Resinchem/Ultimate-Bedside-Lamp/docs/commands.md

---
layout: default
title: Controller Commands
parent: General System Use
nav_order: 3
---

# Controller Commands
{: .no_toc }

---

<p align="center">
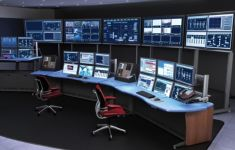
[picture p59: docs/images/commands_01.jpg]
Controller Commands Header
  
</p>

Under normal operation, the system firmware abstracts the hardware so you don't have to worry about which of the three ESP-based controllers you are interacting with. However, **Controller Commands** are the exception—these functions generally apply *only* to the specific controller currently active in your browser.

> **💡 Identifying the Active Controller**<br>As detailed in the [Web Application Overview]({{ '/webapp' | relative_url }}), look for these indicators to know which unit you are controlling:
> * **Primary Controller:** Light Gray background; assigned Device Name in the header.
> * **Display Controller:** Pale Yellow background; "Display" in the header/browser tab.
{: .note }

---

## Primary Controller Commands
These are found at the bottom of the primary controller’s web page. All **yellow** buttons in this section impact only the _primary_ controller.

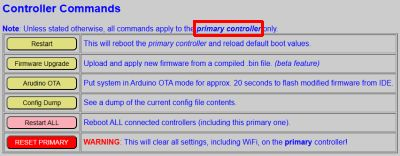
[picture p60: docs/images/commands_02.jpg]
Primary Commands Interface


* **Restart:** Reboots the primary controller only. Other units remain operational, though some cross-device features will pause until the primary unit finishes its boot sequence.

* **Firmware Upgrade:** Accesses the update page for the primary controller. 
    > **⚠️ Warning**<br>Installing the wrong firmware file on the wrong controller will break your system. See [Installing Updates]({{ '/firmwareupdates' | relative_url }}) before proceeding.
    {: .warning }

* **Arduino OTA:** Enables "Over-the-Air" programming for 20 seconds, allowing you to begin flashing code directly from the Arduino IDE. See [Modifying the Firmware]({{ '/modifications' | relative_url }}).
* **Config Dump:** Clicking this will spit out a raw JSON view of your entire configuration. It’s not the prettiest thing to look at, but it is the "Source of Truth" for your lamp’s brain. If a support request asks for your config, this is where you go to prove that you haven't actually programmed the lamp to wake you up at 4:00 AM on a Sunday. 
    * **Config File:** The primary boot values.
    * **Discover File:** Only present if [Home Assistant Discovery]({{ '/discoverymain' | relative_url }}) has been utilized.

### System-Wide Action
* **Restart ALL:** This is the only "global" command. It sends a reboot signal to all three controllers simultaneously to refresh the entire system.

> **❗ HIGH RISK: RESET PRIMARY**<br>This command wipes **ALL** configuration data from the primary controller, including saved Wi-Fi credentials. Use this only if you intend to return the controller to its original installation state. You will have to repeat the [Onboarding]({{ '/onboarding' | relative_url }}) and [System Setup]({{ '/setupmain' | relative_url }}) processes.
{: .warning }

---

## Display Controller Commands
To access these, click the **Display** button from the primary controller’s main menu to switch to the Display Controller interface.

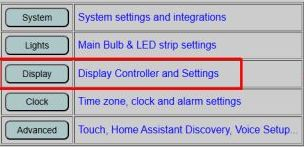
[picture p61: docs/images/dispbrightness_03.jpg]
Accessing Display Menu


The commands are located at the bottom of the display settings page. While the interface is similar, these actions only impact the display hardware.

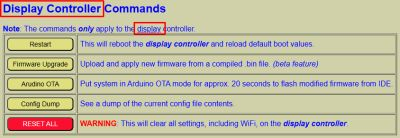
[picture p62: docs/images/commands_03.jpg]
Display Commands Interface


* **Restart / Firmware Upgrade / Arduino OTA:** These operate identically to the primary commands but target only the display controller.
* **Config Dump:** Show a view of all configuration files. The display controller manages three distinct files:
    * **Main Config File:** Primary display and boot settings.
    * **Alarm File:** Saved schedules and alarm preferences.
    * **Sound Library:** Maps track names to physical indices on the microSD card.

> **❗ HIGH RISK: RESET ALL (Display)**<br>This command wipes all display-specific data and Wi-Fi credentials. You will need to onboard and configure the controller again.  If the IP address changes after a reset, you must also update the [System Interface]({{ '/interfaces' | relative_url }}) settings on the primary controller to restore communication.
{: .warning }
---
## External Control
Some of these commands can also be send via MQTT or via the HTTP API.  See * [Using MQTT and the API]({{ '/integrationmain' | relative_url }}) for a list of applicable commands.

<div style="display: flex; justify-content: space-between; align-items: center; margin-top: 40px; border-top: 1px solid #333; padding-top: 20px;">
  <a href="{{ '/dispbrightness' | relative_url }}" class="btn btn-outline"><- Previous: Managing Display Brightness</a>
  <a href="{{ '/alarmmain' | relative_url }}" class="btn btn-purple">Next: Alarms -></a>
</div>
