Resinchem/Ultimate-Bedside-Lamp/docs/usingmain.md

---
layout: default
title: General System Use
nav_order: 5
has_children: true
has_toc: false
---

# General System Use
{: .no_toc }

---

<p align="center">
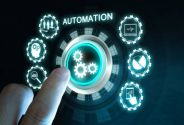
[picture p90: docs/images/usingmain_01a.jpg]
General System Interaction
  
</p>

### Daily Operations

This is where the magic happens. Now that you've done the hard work of flashing, wiring, and configuring, it's time to actually use the thing. Whether you're adjusting colors via the web app or checking the weather from your nightstand, these pages cover the "how-to" of your new bedside companion. No specialized engineering degree required (though it might feel like you earned one by this point). 

> **💡 Active vs. Default Settings**<br>When interacting with the system using the methods covered here, you are primarily changing the system's **ACTIVE** values. These changes reflect the current state of the lamp but will be lost if the system restarts or reboots. To make a change permanent, you must adjust the **DEFAULT** values as covered in [Setting Up the System]({{ '/setupmain' | relative_url }}).
{: .note }

*Note: Detailed instructions for setting and responding to alarms are covered separately under the [Alarms]({{ '/alarmmain' | relative_url }}) section.*

---

### In This Section

* **[Controlling The Lights]({{ '/lightcontrol' | relative_url }})** – Managing both the RGBW bulb and the internal LED strip.
* **[Managing Display Brightness]({{ '/dispbrightness' | relative_url }})** – Adjusting the CYD screen for your environment.
* **[Controller Commands]({{ '/commands' | relative_url }})** – Using specialized system and maintenance commands.

Each of the following pages details the various methods of routinely controlling and interacting with your project components.

---

<div style="display: flex; justify-content: space-between; align-items: center; margin-top: 40px; border-top: 1px solid #333; padding-top: 20px;">
  <a href="{{ '/touchsensors' | relative_url }}" class="btn btn-outline"><- Previous: Touch Sensors</a>
  <a href="{{ '/lightcontrol' | relative_url }}" class="btn btn-purple">Next: Controlling Lights -></a>
</div>
