Resinchem/Ultimate-Bedside-Lamp/docs/images/03Flashing_8_ESPConnect.jpg

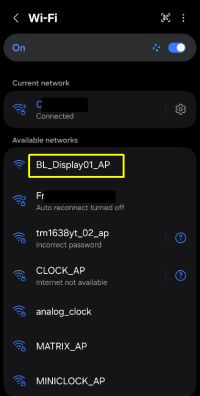
docs/images/03Flashing_8_ESPConnect.jpg
