Resinchem/Ultimate-Bedside-Lamp/docs/images/alarmoptions_04.jpg

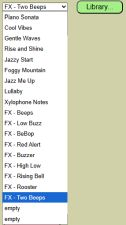
docs/images/alarmoptions_04.jpg
