Resinchem/Ultimate-Bedside-Lamp/docs/images/alarms_04.jpg

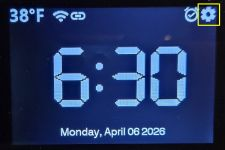
docs/images/alarms_04.jpg
