Resinchem/Ultimate-Bedside-Lamp/docs/images/alarms_06b.jpg

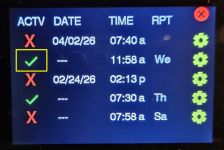
docs/images/alarms_06b.jpg
