Resinchem/Ultimate-Bedside-Lamp/docs/images/alarms_08.jpg

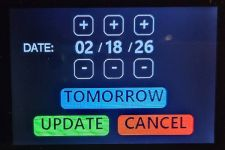
docs/images/alarms_08.jpg
