Resinchem/Ultimate-Bedside-Lamp/docs/images/alarms_09.jpg

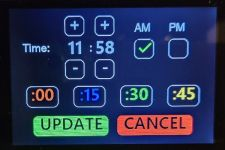
docs/images/alarms_09.jpg
