Resinchem/Ultimate-Bedside-Lamp/docs/images/alarms_10.jpg

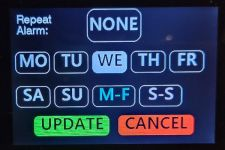
docs/images/alarms_10.jpg
