Resinchem/Ultimate-Bedside-Lamp/docs/images/discoverymain_03.jpg

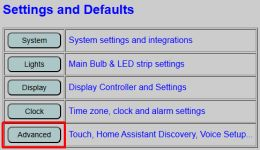
docs/images/discoverymain_03.jpg
