Resinchem/Ultimate-Bedside-Lamp/docs/images/discoverymain_05a.jpg

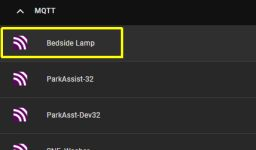
docs/images/discoverymain_05a.jpg
