Resinchem/Ultimate-Bedside-Lamp/docs/images/discoverymain_11.jpg

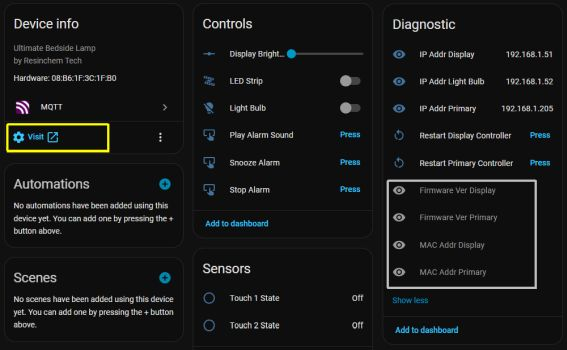
docs/images/discoverymain_11.jpg
