Resinchem/Ultimate-Bedside-Lamp/docs/images/discoverymain_15.jpg

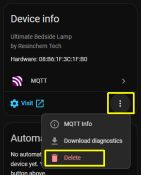
docs/images/discoverymain_15.jpg
