Resinchem/Ultimate-Bedside-Lamp/docs/images/imagehold.jpg

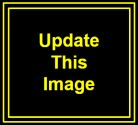
docs/images/imagehold.jpg
