Resinchem/Ultimate-Bedside-Lamp/docs/images/time_06a.jpg

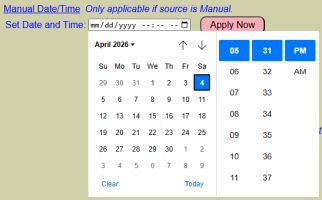
docs/images/time_06a.jpg
