Resinchem/Ultimate-Bedside-Lamp/docs/images/weather_05.jpg

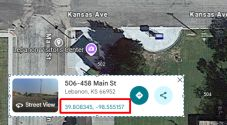
docs/images/weather_05.jpg
