Resinchem/Ultimate-Bedside-Lamp/src/display/icons20pt7b.h

const uint8_t icomoon20pt7bBitmaps[] PROGMEM = {
  0x00, 0x7B, 0xDE, 0xF7, 0xBD, 0xEF, 0x7B, 0xDE, 0xF7, 0xBD, 0xEF, 0x7B,
  0xDE, 0x00, 0x00, 0x0E, 0xFF, 0xFE, 0xE0, 0xE1, 0xFC, 0x3F, 0x87, 0xF0,
  0xFE, 0x1F, 0xC3, 0xF8, 0x7F, 0x0F, 0x00, 0xE0, 0xE0, 0x03, 0x87, 0x00,
  0x1E, 0x1C, 0x00, 0x70, 0x70, 0x01, 0xC1, 0xC0, 0x07, 0x07, 0x00, 0x1C,
  0x3C, 0x00, 0x70, 0xE0, 0x3F, 0xFF, 0xF9, 0xFF, 0xFF, 0xE0, 0x38, 0x78,
  0x00, 0xE1, 0xC0, 0x07, 0x07, 0x00, 0x1C, 0x1C, 0x00, 0x70, 0x70, 0x3F,
  0xFF, 0xFC, 0xFF, 0xFF, 0xF0, 0x38, 0x38, 0x00, 0xE0, 0xE0, 0x03, 0x87,
  0x80, 0x0E, 0x1C, 0x00, 0x70, 0x70, 0x01, 0xC1, 0xC0, 0x07, 0x07, 0x00,
  0x1C, 0x3C, 0x00, 0x01, 0x80, 0x00, 0xC0, 0x01, 0xFF, 0x03, 0xFF, 0xC3,
  0xFF, 0xE3, 0xFF, 0xF1, 0xF6, 0x19, 0xF3, 0x00, 0xF1, 0x80, 0x78, 0xC0,
  0x3C, 0x60, 0x1F, 0x30, 0x07, 0x98, 0x03, 0xFC, 0x00, 0xFE, 0x00, 0x3F,
  0xC0, 0x07, 0xF8, 0x00, 0xFE, 0x00, 0x7F, 0x80, 0x33, 0xE0, 0x18, 0xF8,
  0x0C, 0x3C, 0x06, 0x1E, 0x03, 0x0F, 0x81, 0x8F, 0xF8, 0xDF, 0xBF, 0xFF,
  0xDF, 0xFF, 0xC7, 0xFF, 0x80, 0xFF, 0x00, 0x06, 0x00, 0x03, 0x00, 0x01,
  0x80, 0x00, 0xC0, 0x00, 0x0F, 0xC0, 0x03, 0x81, 0xFF, 0x00, 0x38, 0x1E,
  0x3C, 0x03, 0x80, 0xE0, 0xE0, 0x1C, 0x0E, 0x03, 0x81, 0xC0, 0x70, 0x1C,
  0x1C, 0x03, 0x80, 0xE0, 0xE0, 0x1C, 0x07, 0x0E, 0x00, 0xE0, 0x38, 0x70,
  0x07, 0x01, 0xC7, 0x00, 0x1C, 0x1C, 0x70, 0x00, 0xF1, 0xE3, 0x80, 0x03,
  0xFE, 0x38, 0x00, 0x07, 0xC3, 0x80, 0x00, 0x00, 0x1C, 0x00, 0x00, 0x01,
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
  {  1848,  15,  28,  21,    4,  -32 },   // 0x46 'F'
  {  1901,  23,  28,  28,    2,  -32 },   // 0x47 'G'
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

const GFXfont icomoon20pt7b PROGMEM = {
  (uint8_t  *)icomoon20pt7bBitmaps,
  (GFXglyph *)icomoon20pt7bGlyphs,
  0x20, 0x7E, 39 };

// Approx. 5967 bytes
